gituser-rk/cmk_livestatus_trafficlight/pics/5.jpg

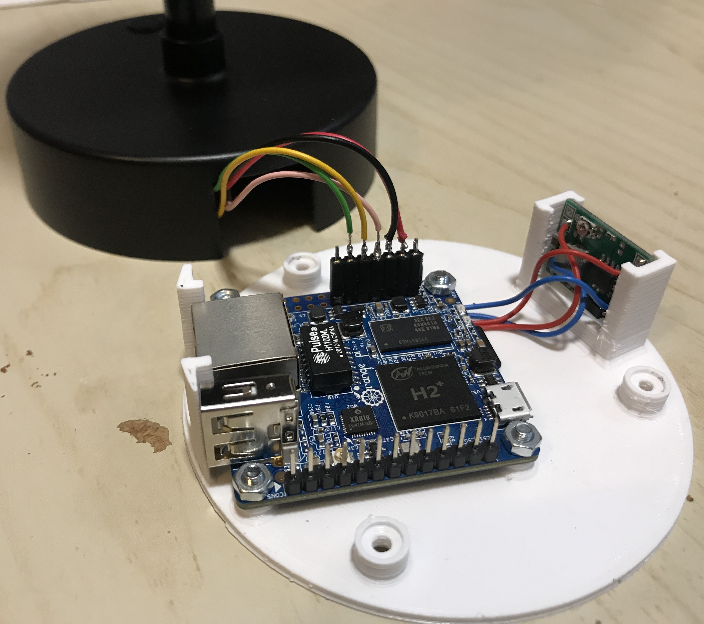
pics/5.jpg
